Duds/OI-Piranha/10. Frame/Battery frame.png

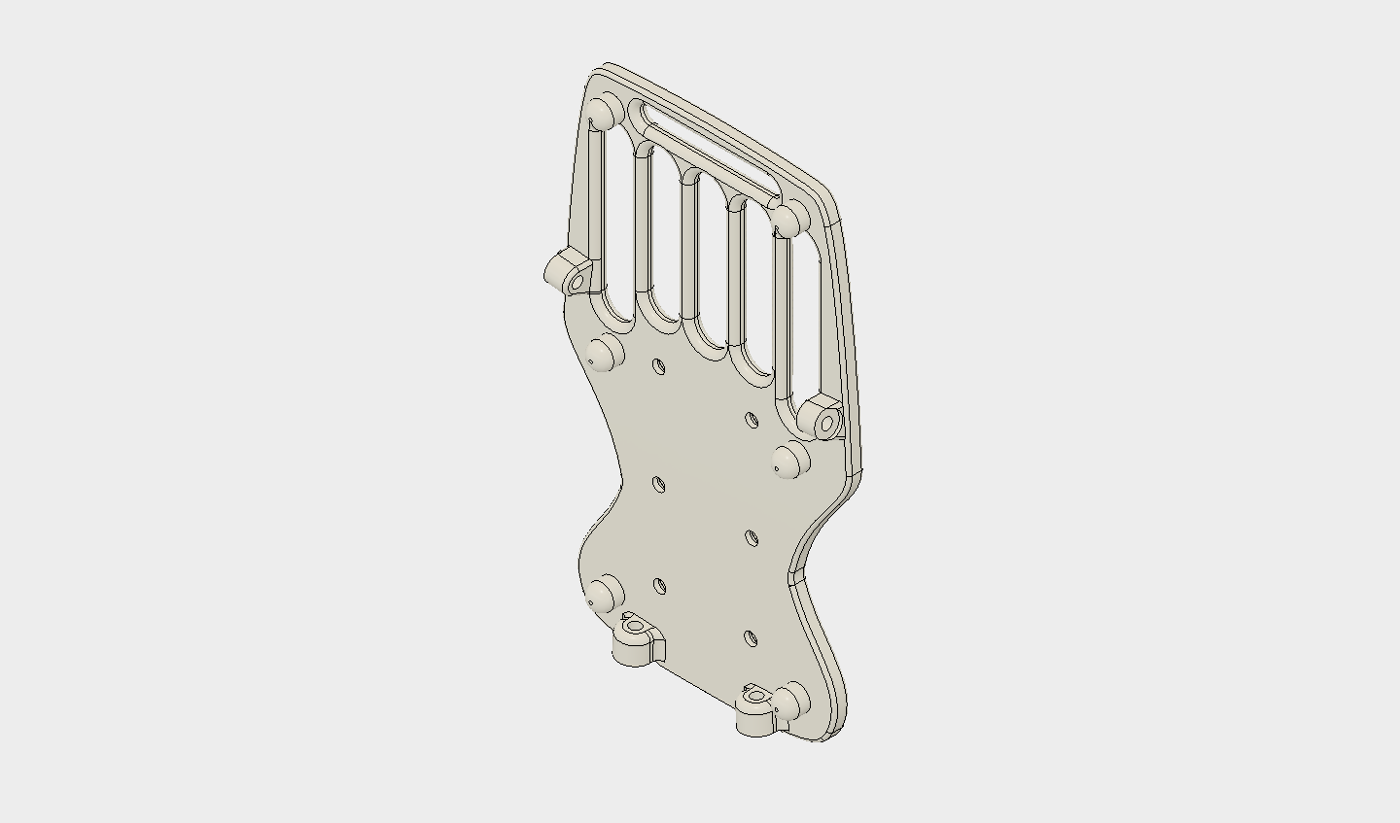
10. Frame/Battery frame.png
