Duds/OI-Piranha/10. Frame/Main frame.png

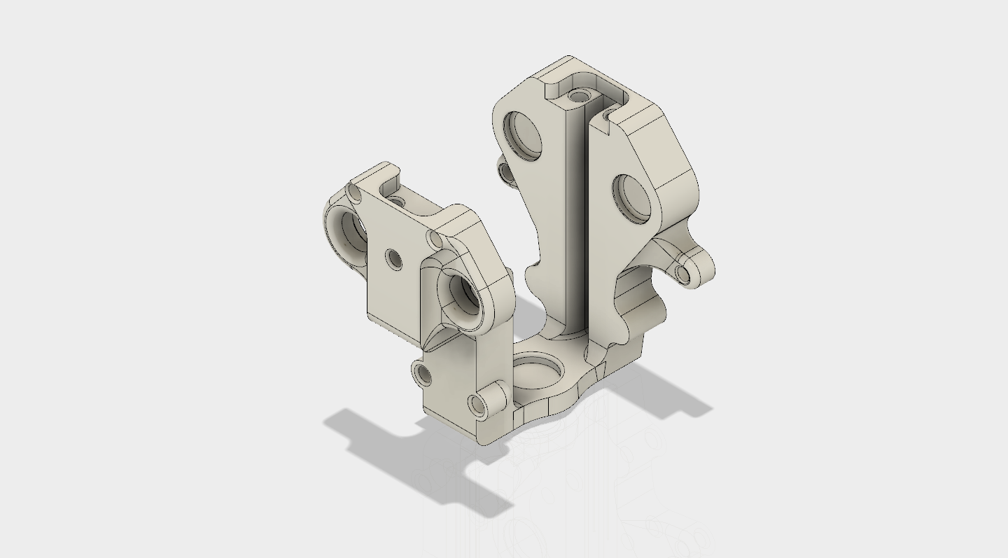
10. Frame/Main frame.png
