Duds/OI-Piranha/10. Frame/Servo Caddy Top Mount.png

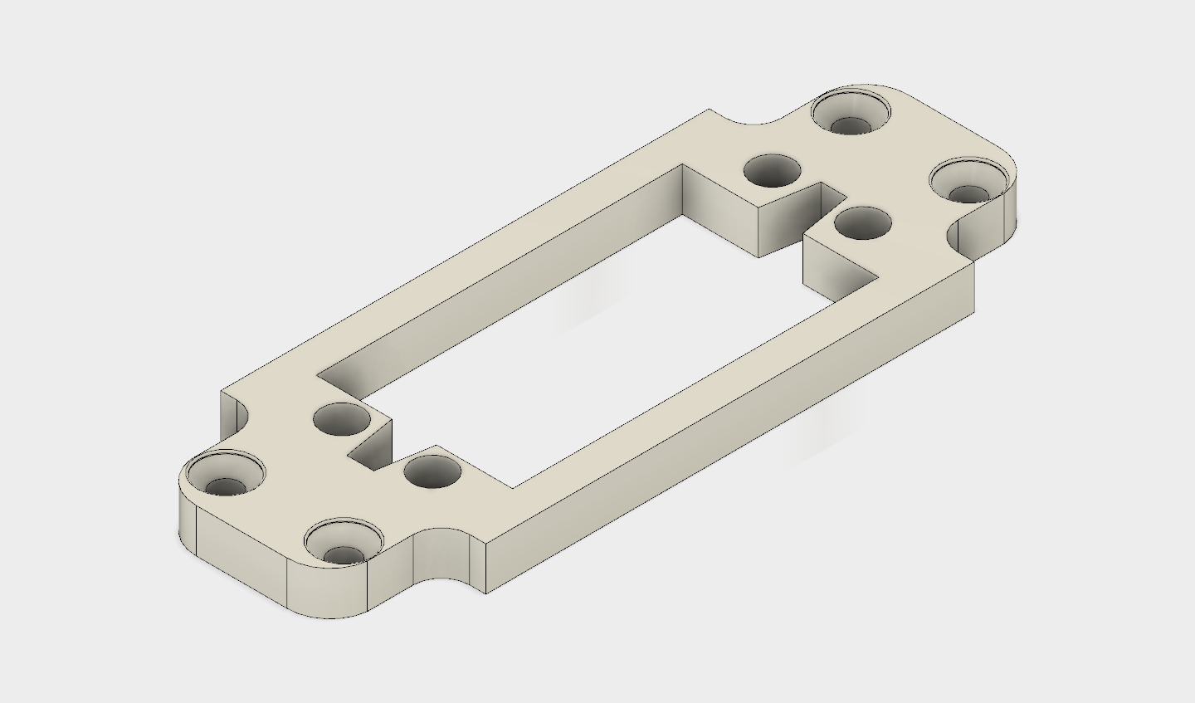
10. Frame/Servo Caddy Top Mount.png
