Duds/OI-Piranha/10. Frame/Servo Caddy.png

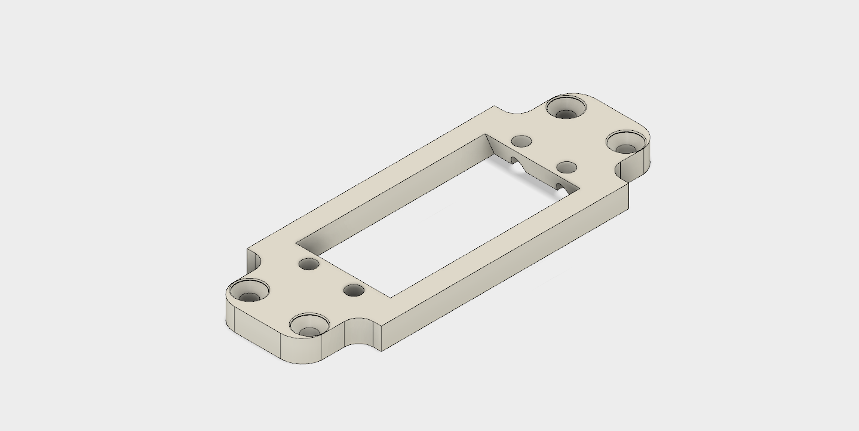
10. Frame/Servo Caddy.png
