Duds/OI-Piranha/20. Body Lift/Lead Screw (buttress thread).png

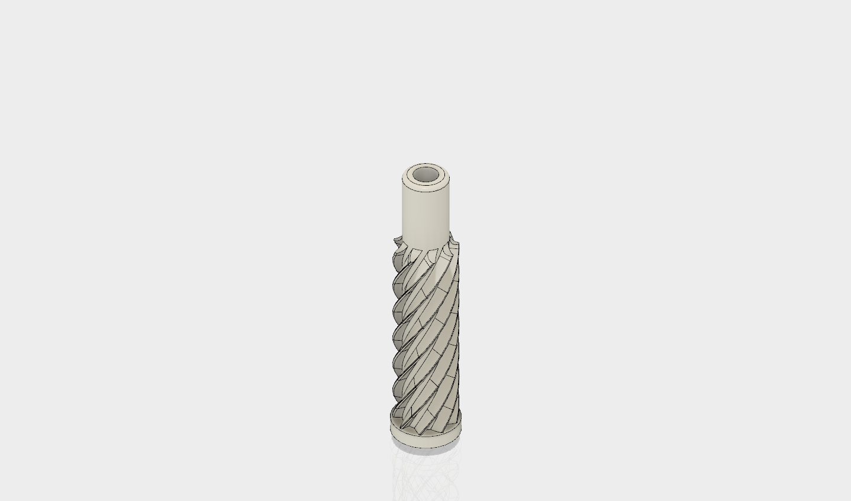
20. Body Lift/Lead Screw (buttress thread).png
