Duds/OI-Piranha/20. Body Lift/Lifting Beam (buttress thread).png

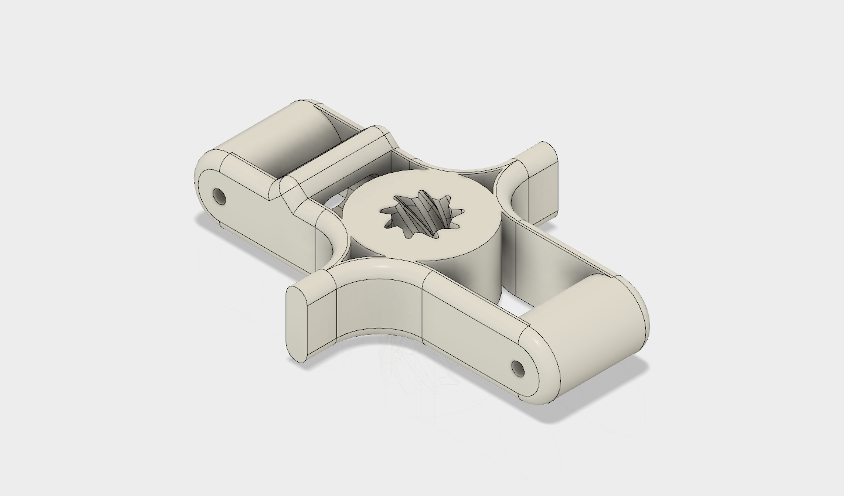
20. Body Lift/Lifting Beam (buttress thread).png
