Duds/OI-Piranha/20. Body Lift/Lifting beam.png

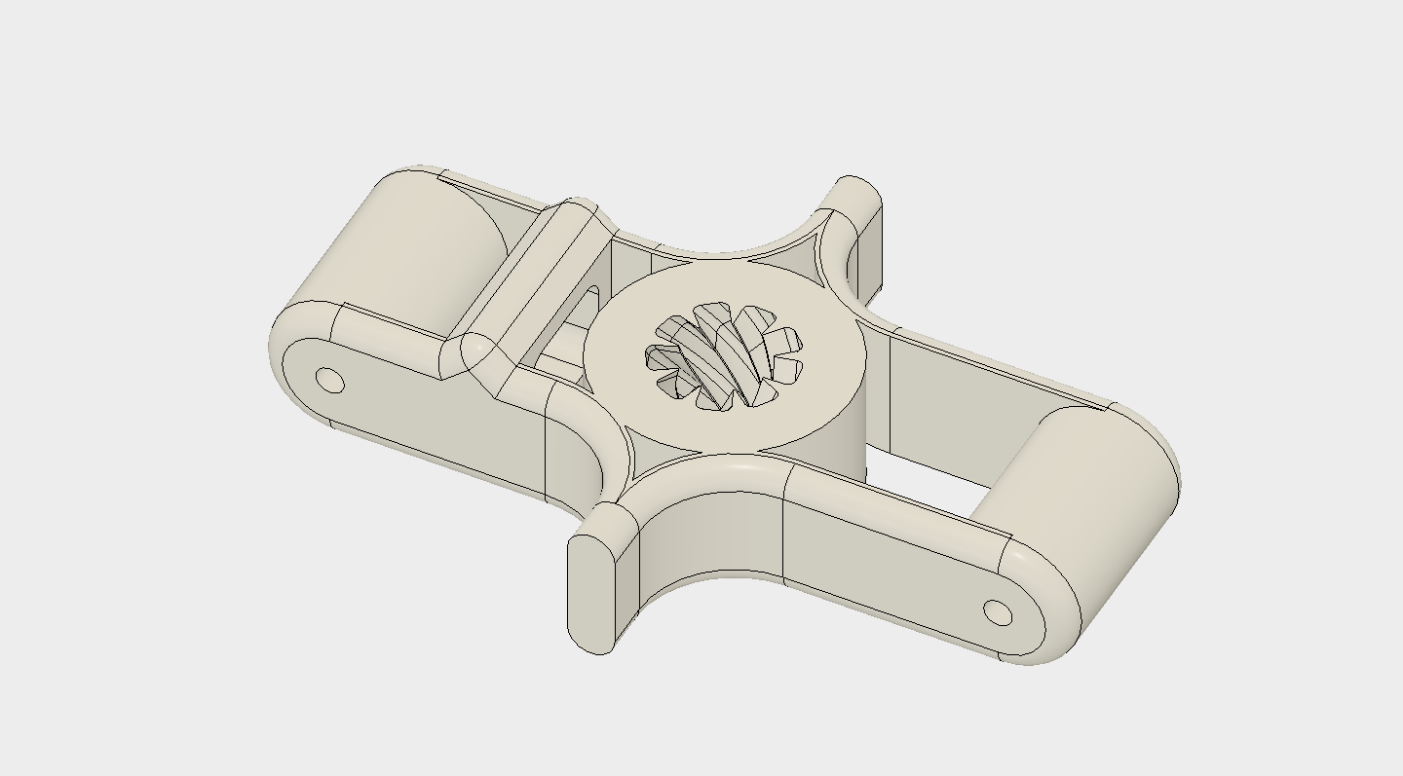
20. Body Lift/Lifting beam.png
