Duds/OI-Piranha/20. Body Lift/Nut die.png

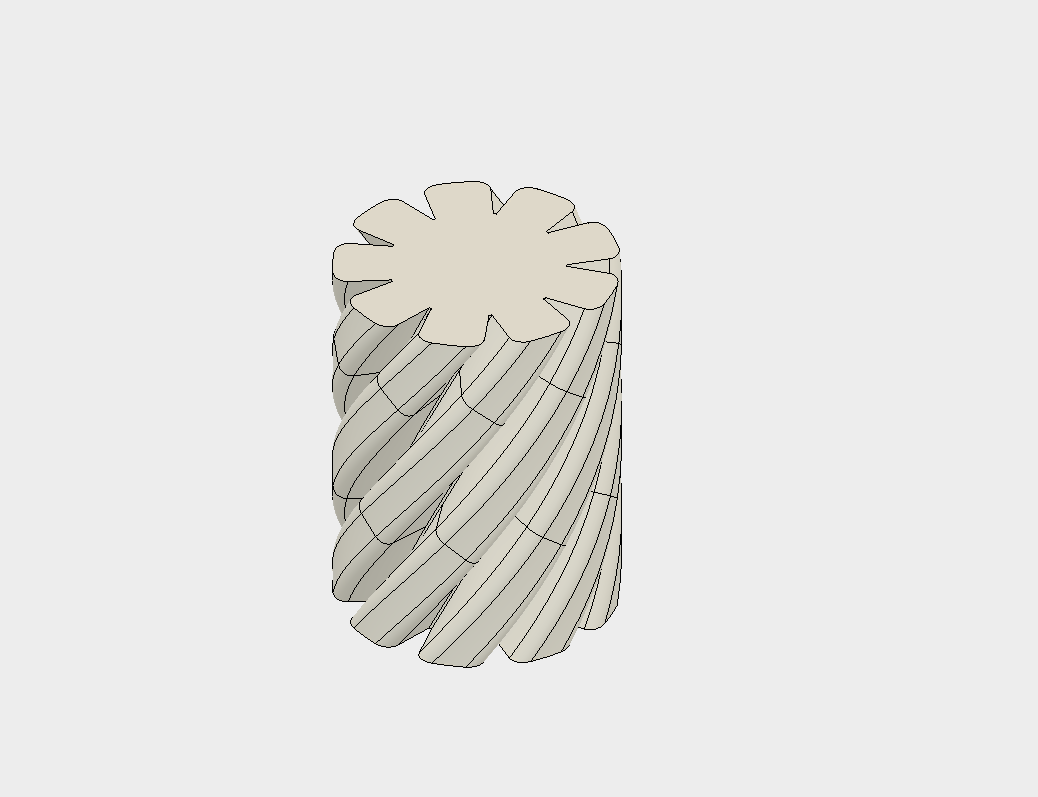
20. Body Lift/Nut die.png
