Duds/OI-Piranha/30. Booms/Landing gear pivot.png

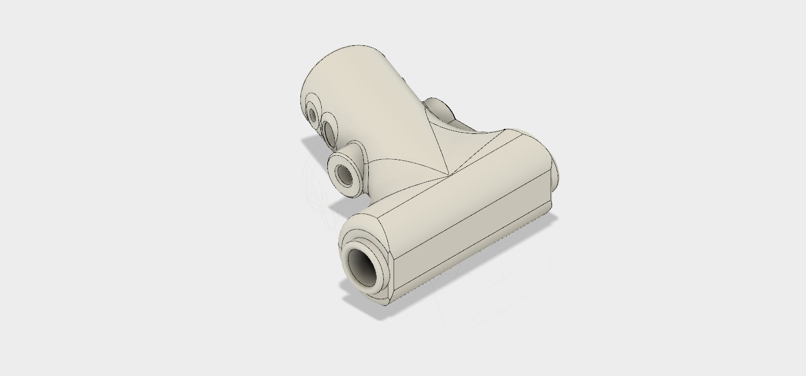
30. Booms/Landing gear pivot.png
