Duds/OI-Piranha/30. Booms/Lift linkage A.png

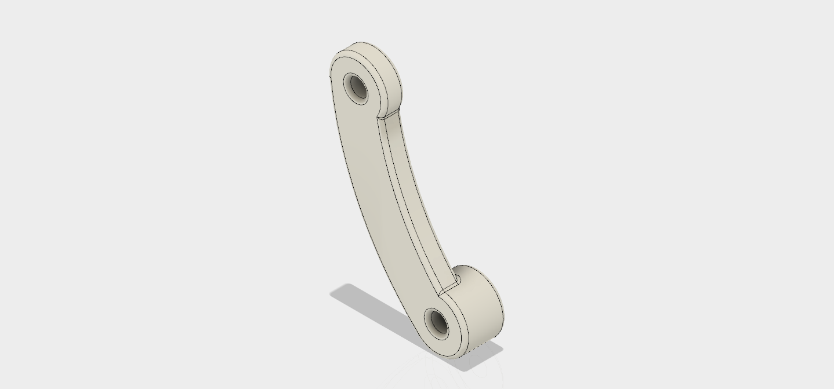
30. Booms/Lift linkage A.png
