Duds/OI-Piranha/50. Fairings/50.1 two part fairing/Bash Plate Two Part.png

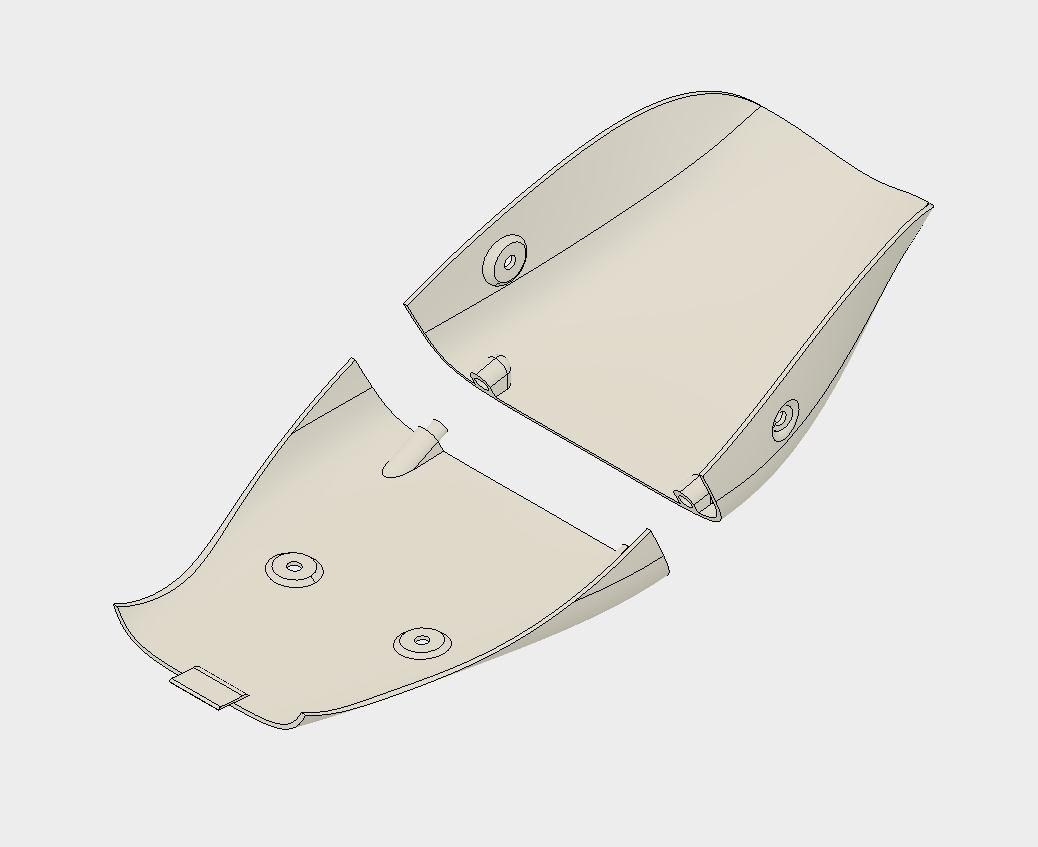
50. Fairings/50.1 two part fairing/Bash Plate Two Part.png
