Duds/OI-Piranha/50. Fairings/50.1 two part fairing/Nose fairing two part no 2.png

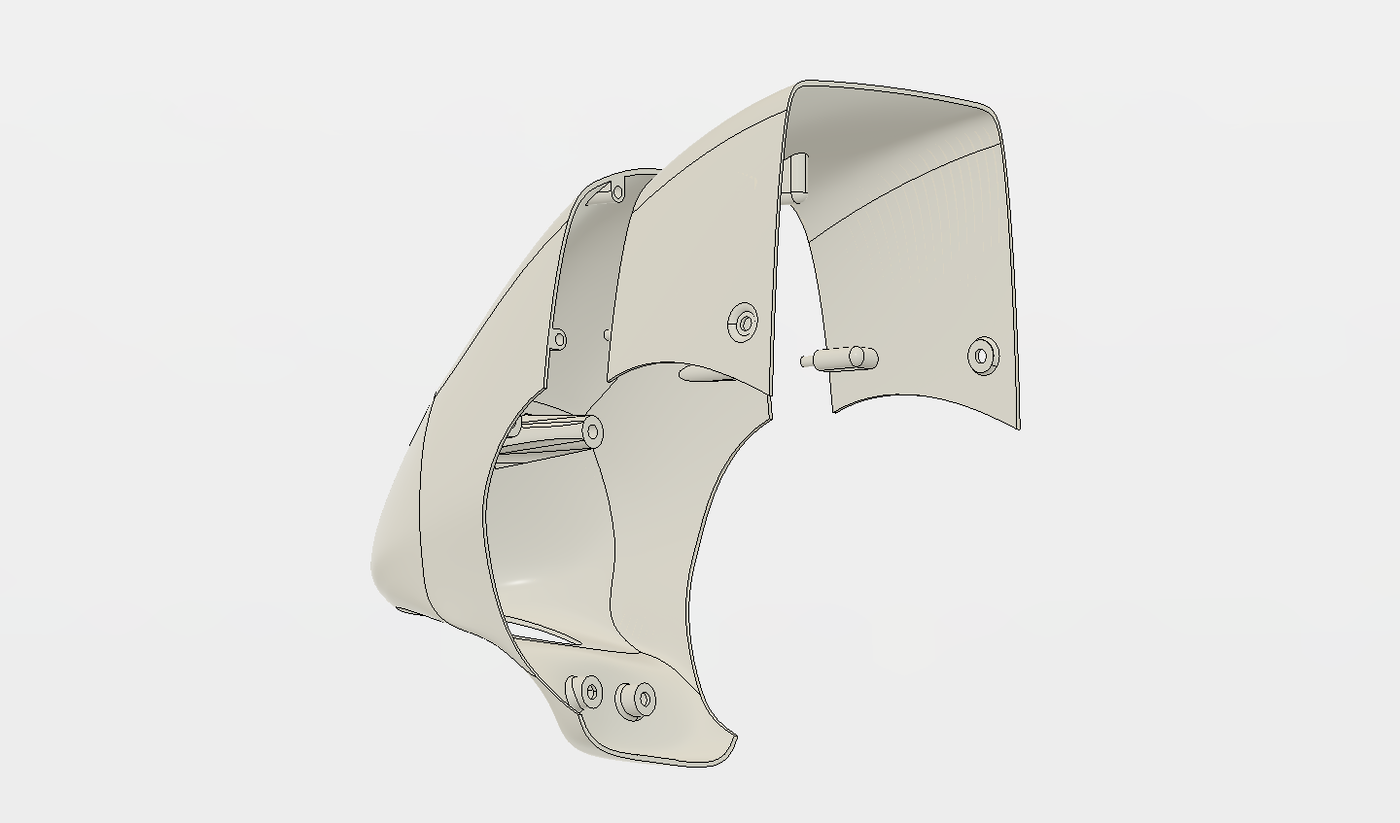
50. Fairings/50.1 two part fairing/Nose fairing two part no 2.png
