Duds/OI-Piranha/50. Fairings/Bash Plate.png

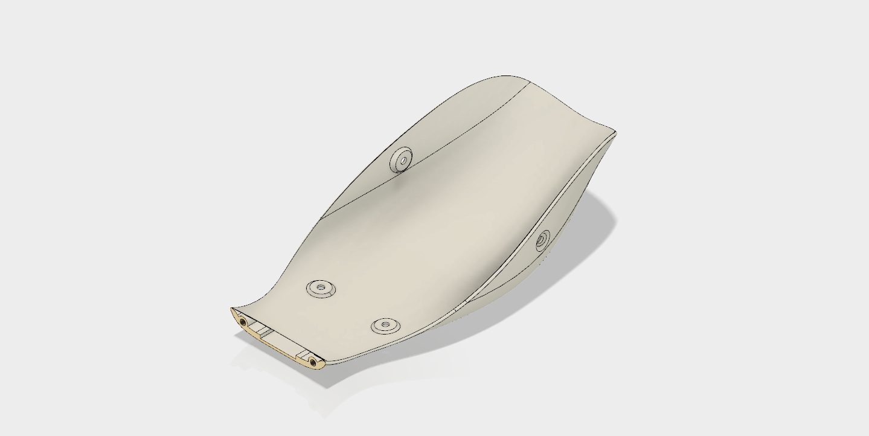
50. Fairings/Bash Plate.png
