Duds/OI-Piranha/50. Fairings/Battery fairing.png

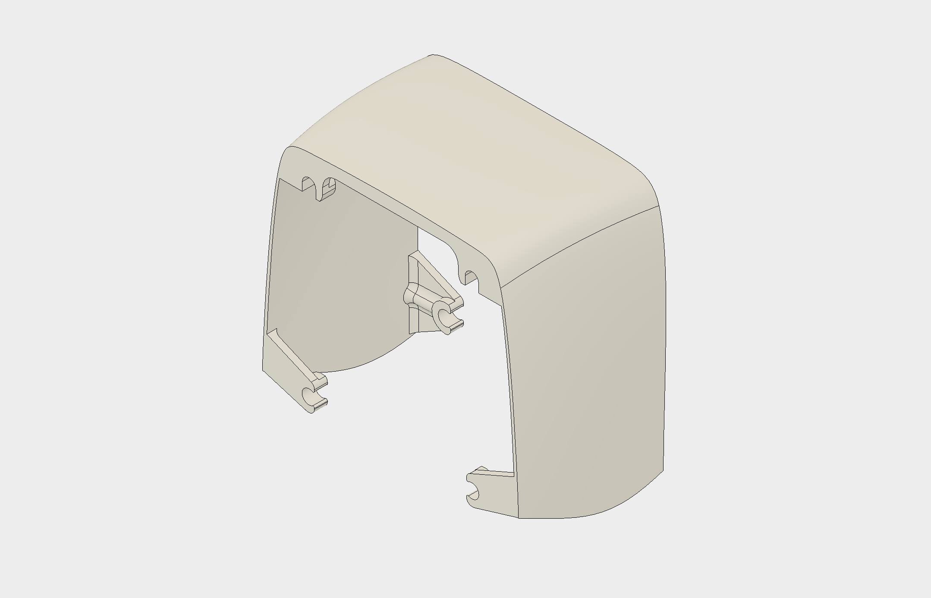
50. Fairings/Battery fairing.png
