Duds/OI-Piranha/50. Fairings/Expansion fairing.png

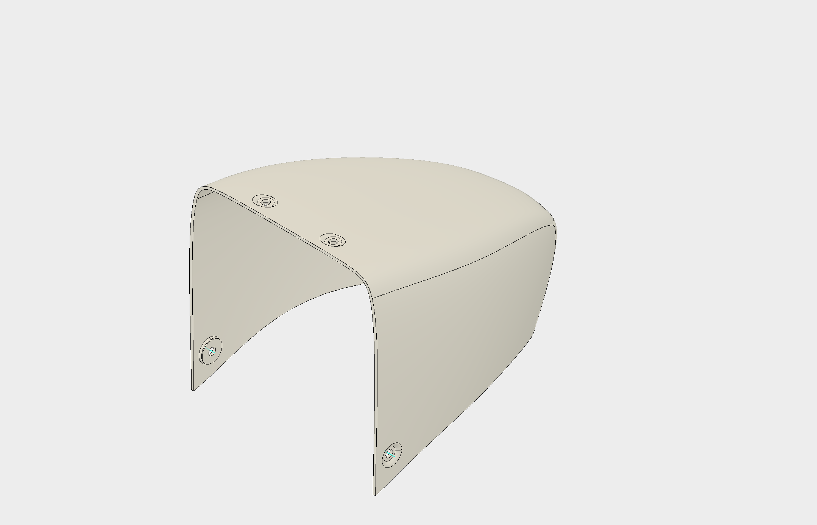
50. Fairings/Expansion fairing.png
