Duds/OI-Piranha/50. Fairings/Nose Fairing.png

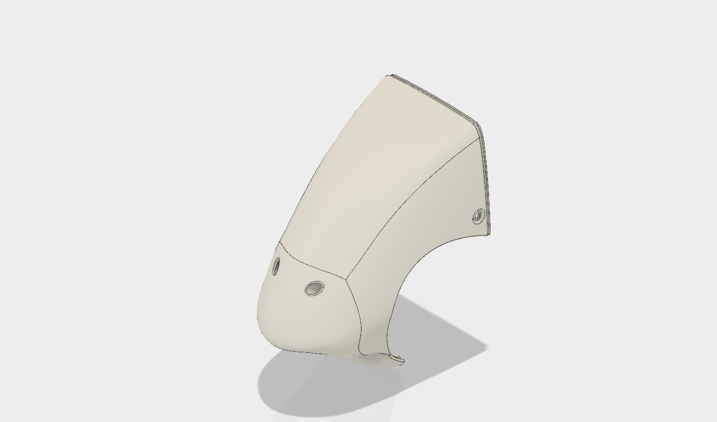
50. Fairings/Nose Fairing.png
