Duds/OI-Piranha/60. Payload/Gimbal support.png

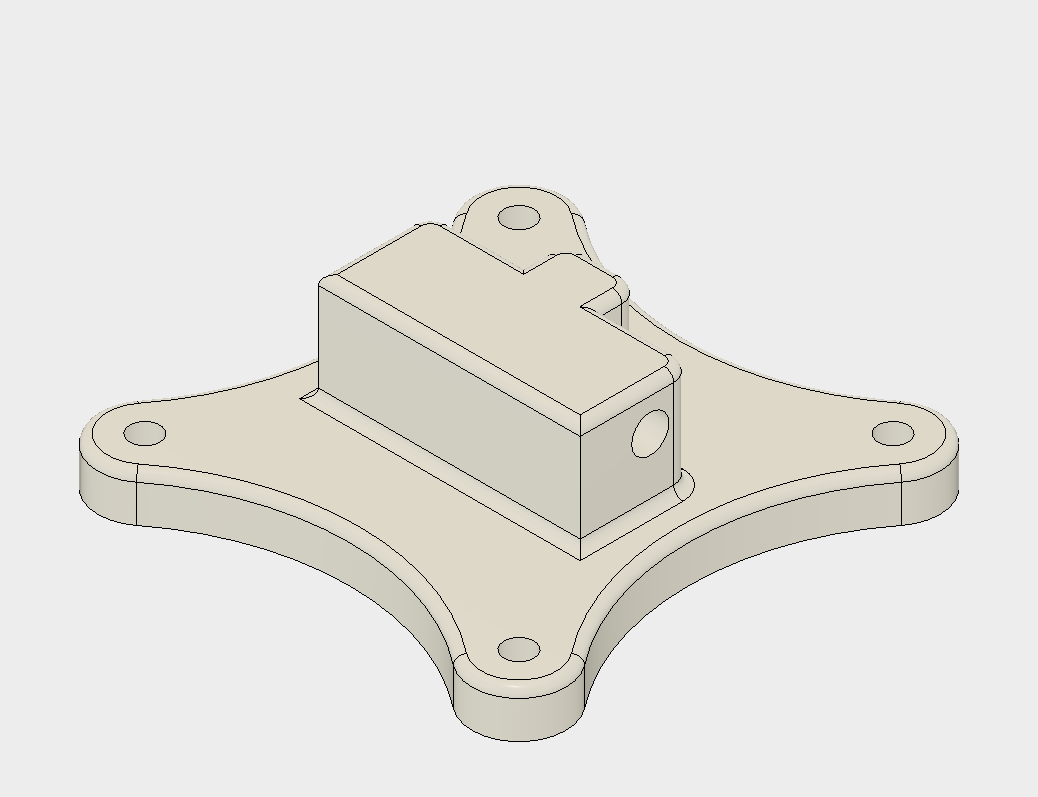
60. Payload/Gimbal support.png
