Duds/OI-Piranha/200. Renders/OI Pirahna expansion shelves.png

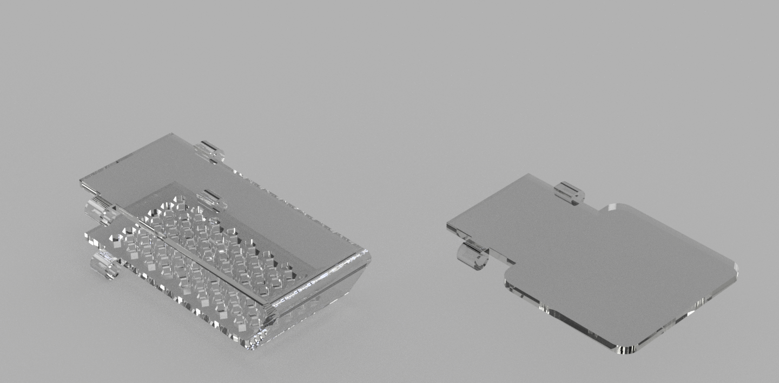
200. Renders/OI Pirahna expansion shelves.png
