Duds/OI-Piranha/200. Renders/OI Pirahna Main frame, caddy and servo.png

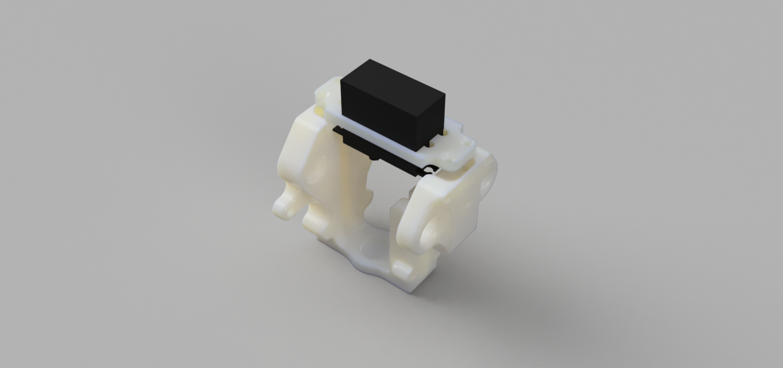
200. Renders/OI Pirahna Main frame, caddy and servo.png
