Duds/OI-Piranha/200. Renders/OI Piranha battery and accessory fairing removed 2.png

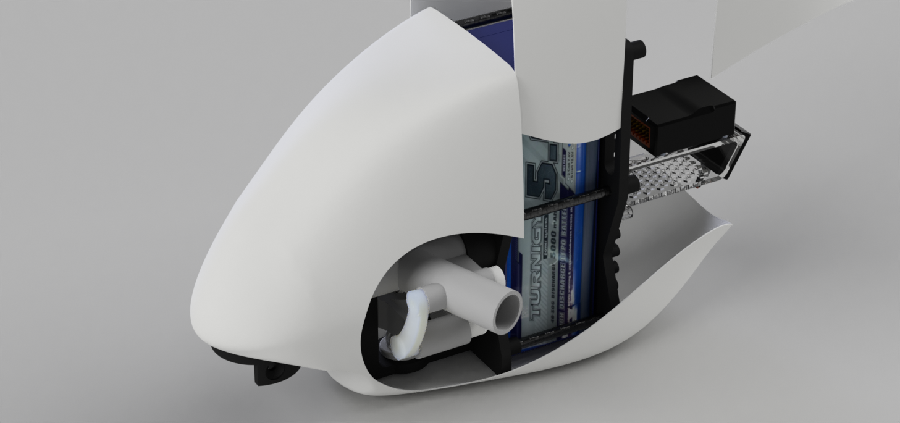
200. Renders/OI Piranha battery and accessory fairing removed 2.png
