Duds/OI-Piranha/200. Renders/OI Piranha battery and accessory fairing removed.png

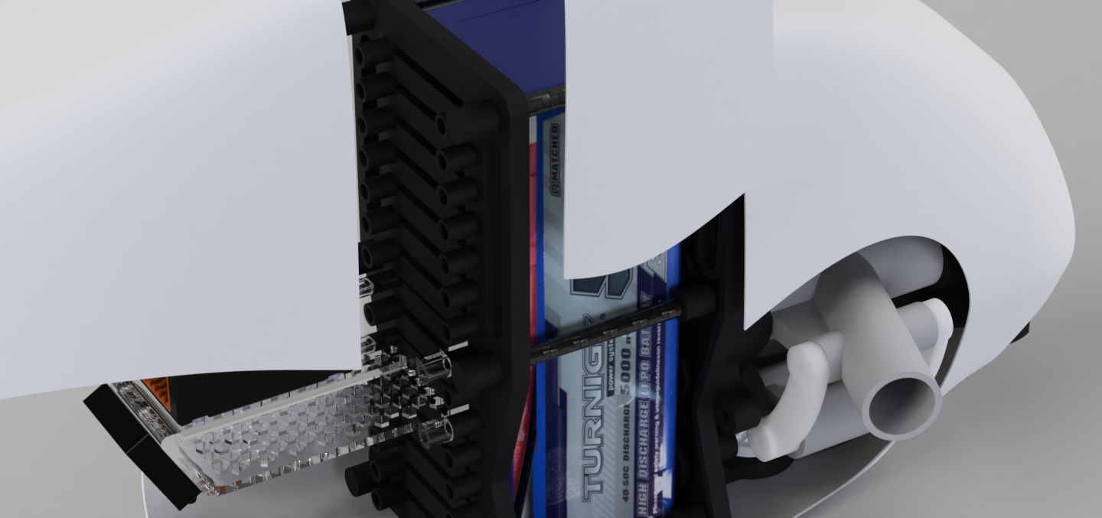
200. Renders/OI Piranha battery and accessory fairing removed.png
