Duds/OI-Piranha/200. Renders/OI Piranha body lift mechanism closeup.png

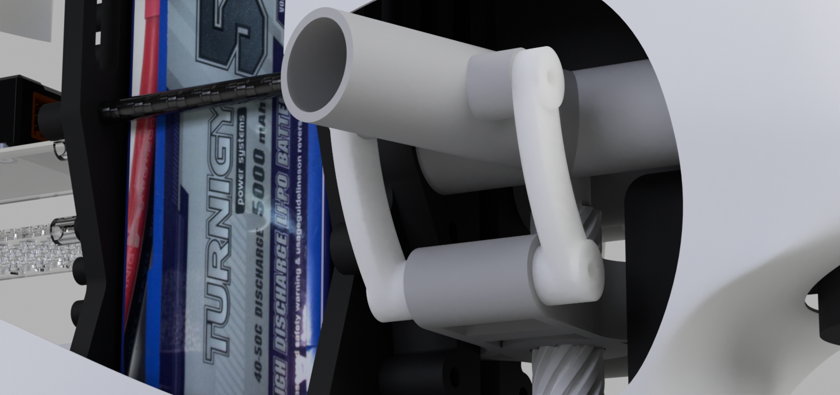
200. Renders/OI Piranha body lift mechanism closeup.png
