Duds/OI-Piranha/200. Renders/OI Piranha close up of NAZA accessory shelf.png

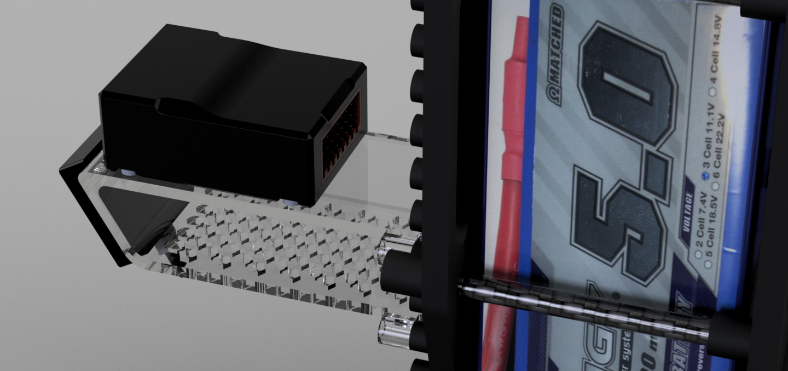
200. Renders/OI Piranha close up of NAZA accessory shelf.png
