Duds/OI-Piranha/200. Renders/OI Piranha closeup NAZA accessory shelf.png

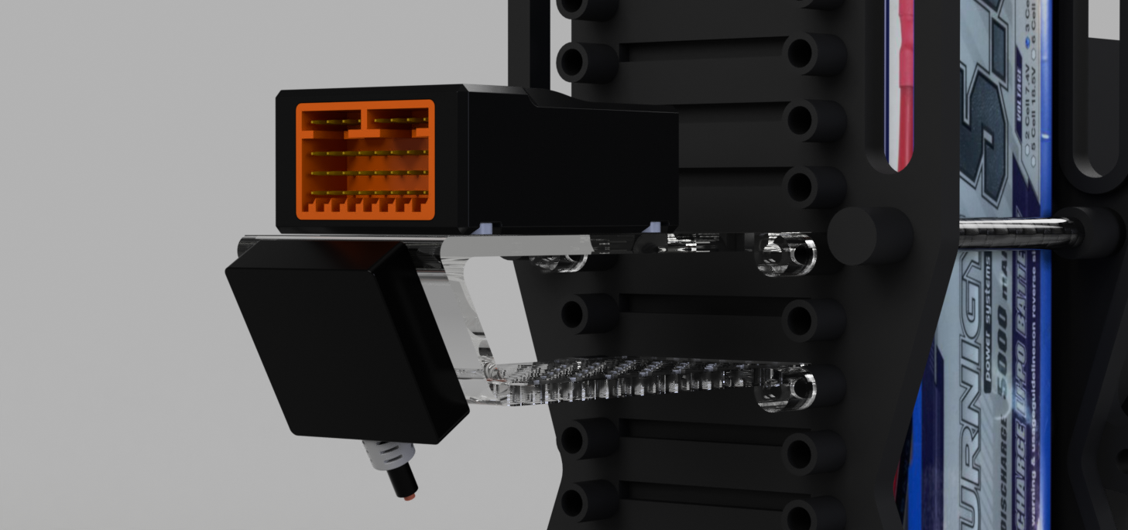
200. Renders/OI Piranha closeup NAZA accessory shelf.png
