Duds/OI-Piranha/200. Renders/OI Piranha Fairings removed.png

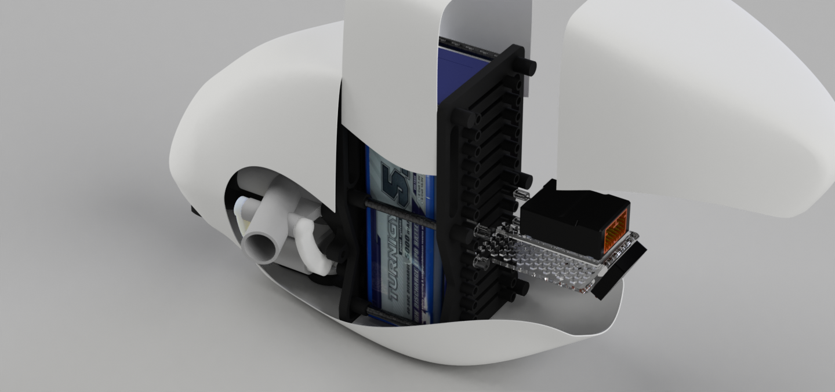
200. Renders/OI Piranha Fairings removed.png
