Duds/OI-Piranha/200. Renders/OI Piranha Frame.png

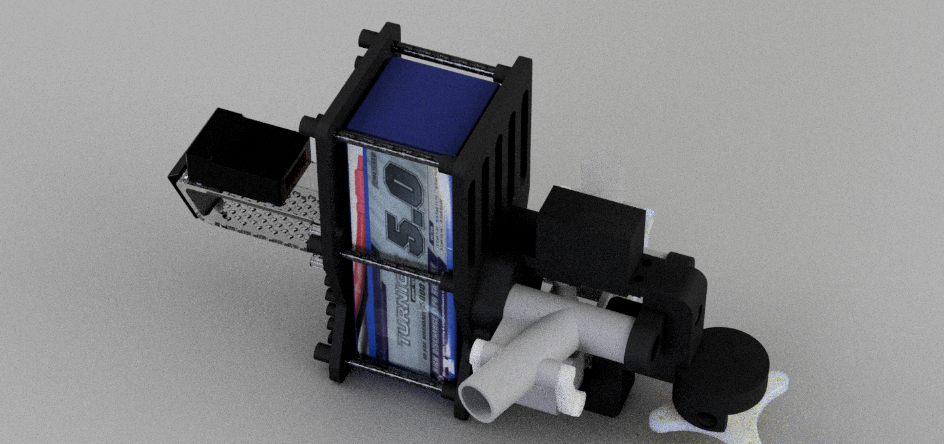
200. Renders/OI Piranha Frame.png
