Duds/OI-Piranha/200. Renders/OI Piranha open frame front.png

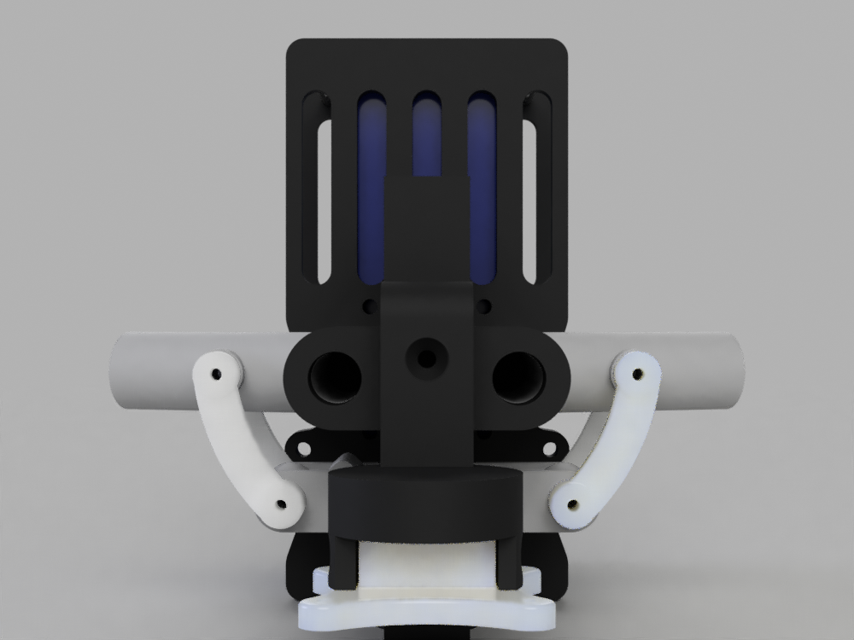
200. Renders/OI Piranha open frame front.png
