Duds/OI-Piranha/200. Renders/OI Piranha open frame side top view.png

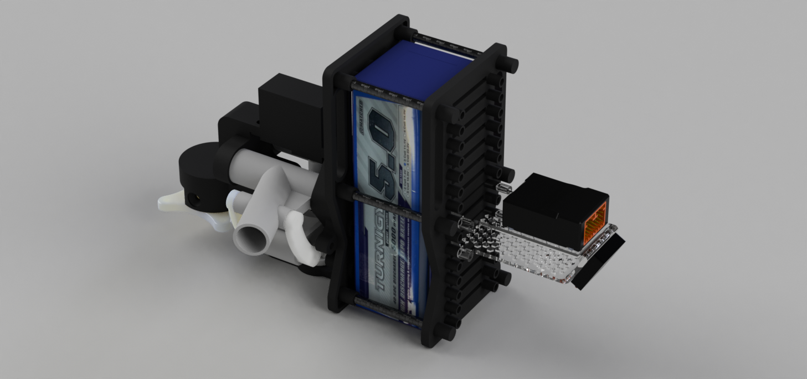
200. Renders/OI Piranha open frame side top view.png
