Duds/OI-Piranha/200. Renders/OI Piranha side view top down.png

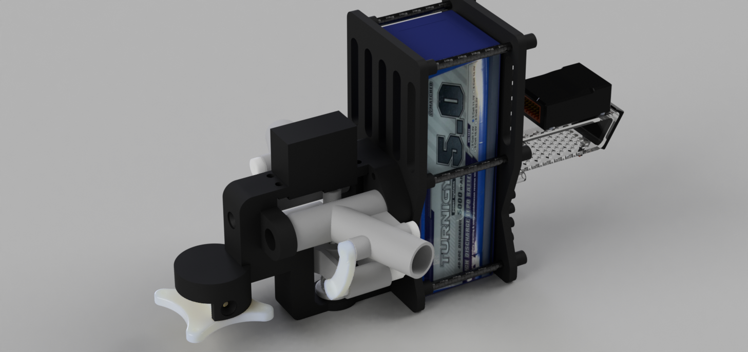
200. Renders/OI Piranha side view top down.png
