Duds/OI-Piranha/200. Renders/OI Piranha v0.3.0 Release image 8.png

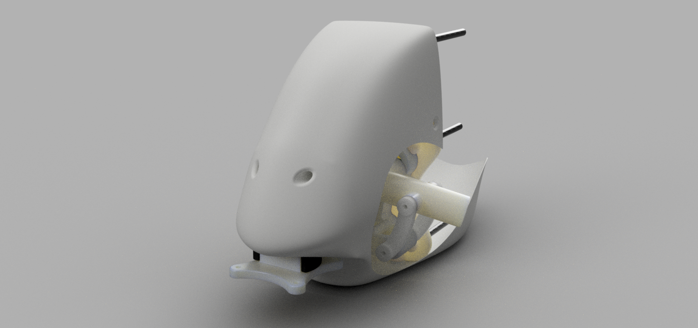
200. Renders/OI Piranha v0.3.0 Release image 8.png
