Duds/OI-Piranha/200. Renders/OI Piranha with fairing on.png

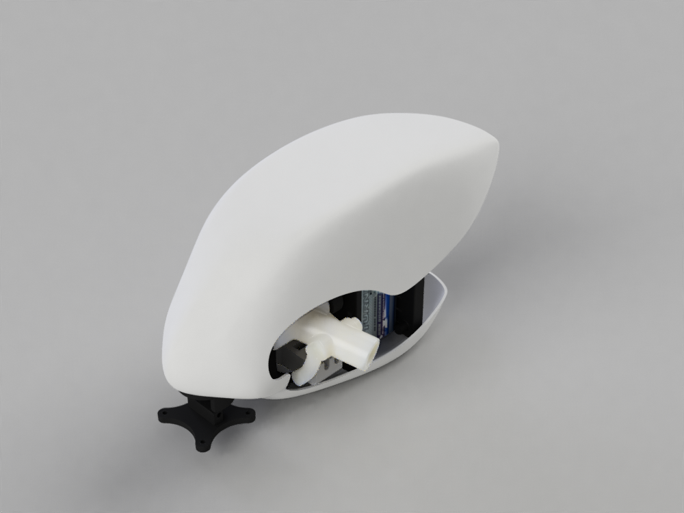
200. Renders/OI Piranha with fairing on.png
