Duds/OI-Piranha/40. Expansion Parts/Basic Expansion Shelf.png

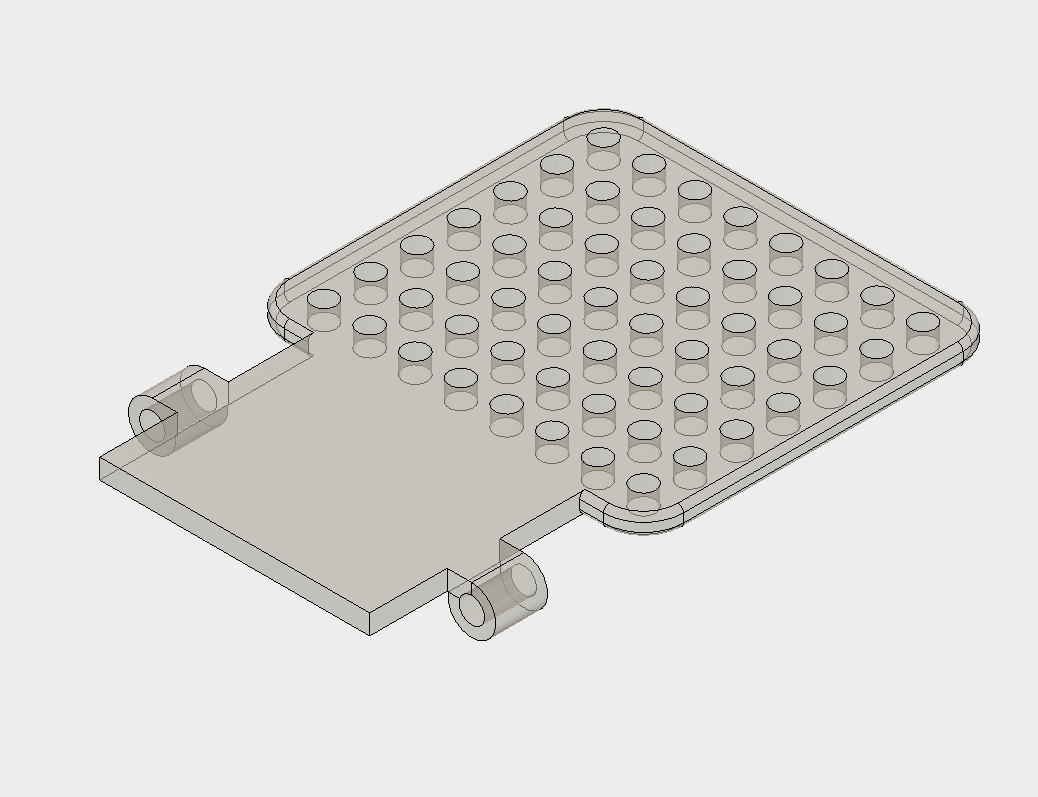
40. Expansion Parts/Basic Expansion Shelf.png
