Duds/OI-Piranha/30. Booms/Landing gear pivot.step

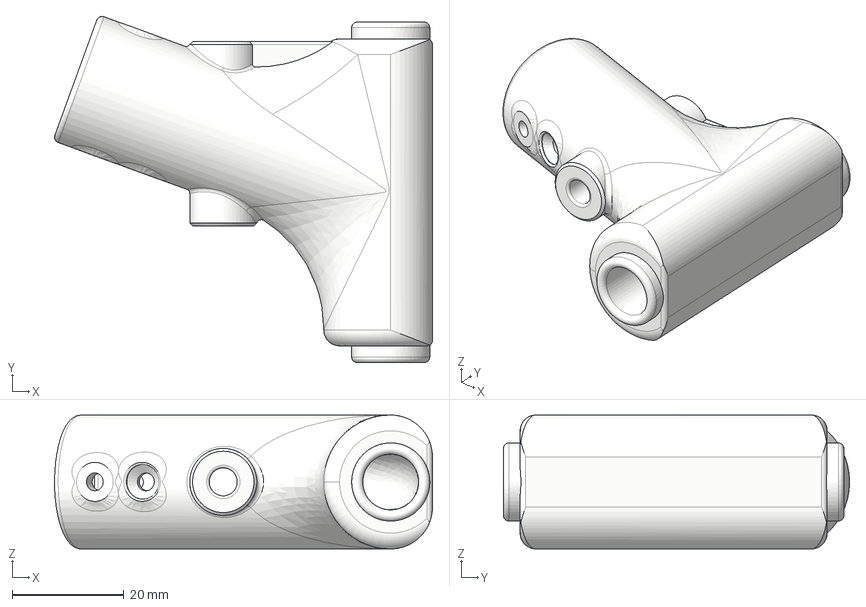
[picture p59: CAD file, 2016-10-27]
30. Booms/Landing gear pivot.step
67.7 x 62.0 x 24.0 mm
