Duds/OI-Piranha/40. Expansion Parts/Basic Expansion Shelf.step

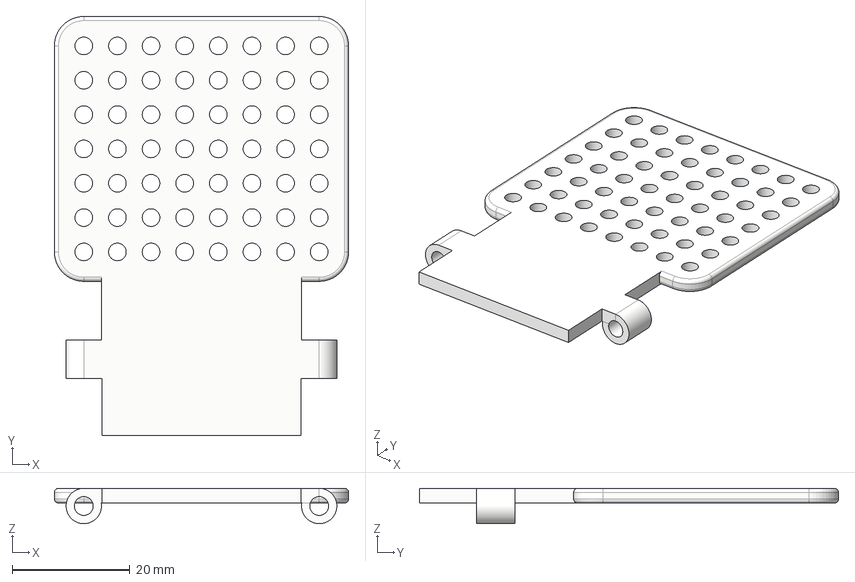
[picture p60: CAD file, 2016-10-15]
40. Expansion Parts/Basic Expansion Shelf.step
50.0 x 71.2 x 6.00 mm
