Duds/OI-Piranha/50. Fairings/50.1 two part fairing/Bash Plate part A.stl

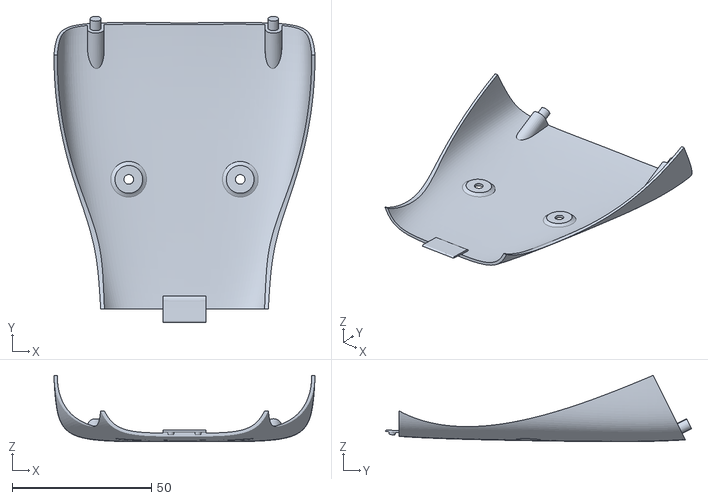
[picture p61: CAD file, 2016-10-15]
50. Fairings/50.1 two part fairing/Bash Plate part A.stl
93.8 x 110.1 x 23.8
