Duds/OI-Piranha/50. Fairings/Battery fairing.step

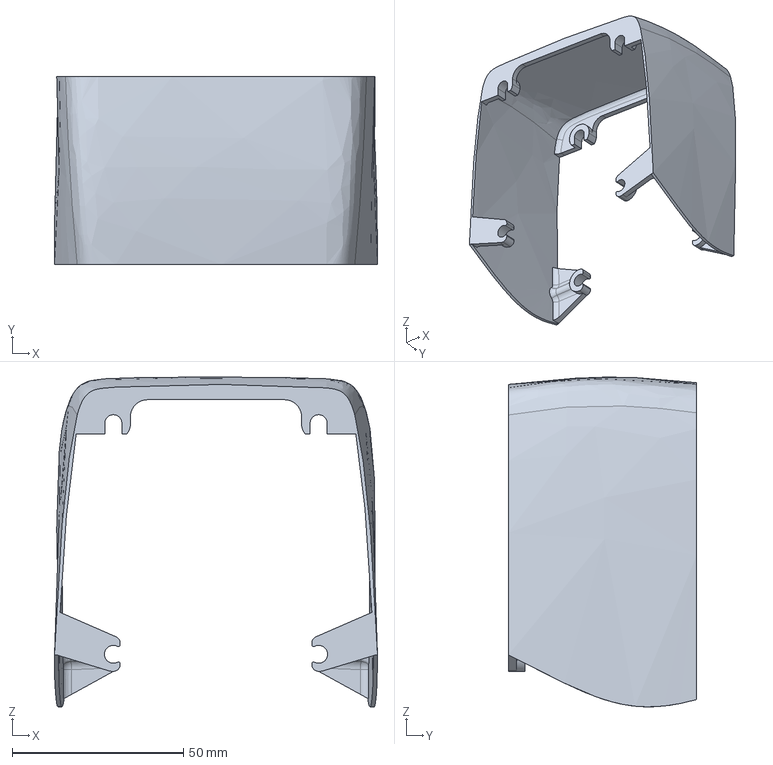
[picture p62: CAD file, 2016-10-15]
50. Fairings/Battery fairing.step
94.4 x 55.0 x 96.4 mm
