Duds/OI-Piranha/10. Frame/10.1 Two Part Frames (for smaller print volumes)/Lifting beam.step

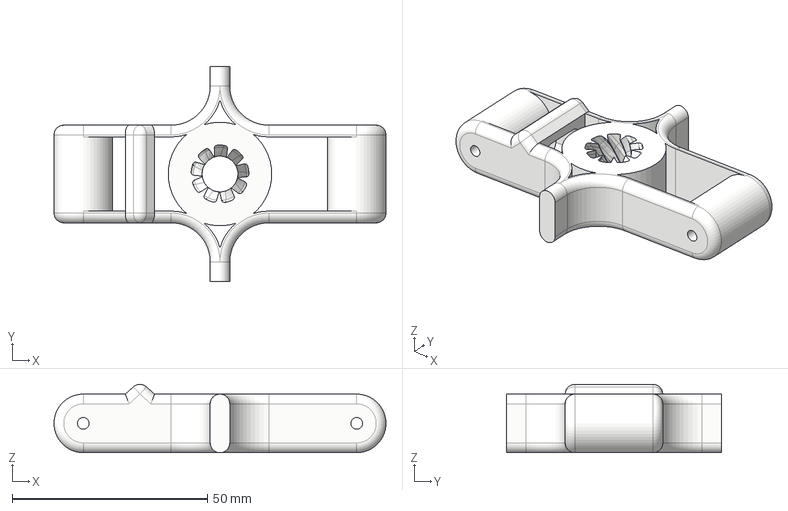
[picture p63: CAD file, 2016-10-15]
10. Frame/10.1 Two Part Frames (for smaller print volumes)/Lifting beam.step
85.0 x 55.0 x 17.5 mm
