Duds/OI-Piranha/10. Frame/Servo Caddy Top Mount.step

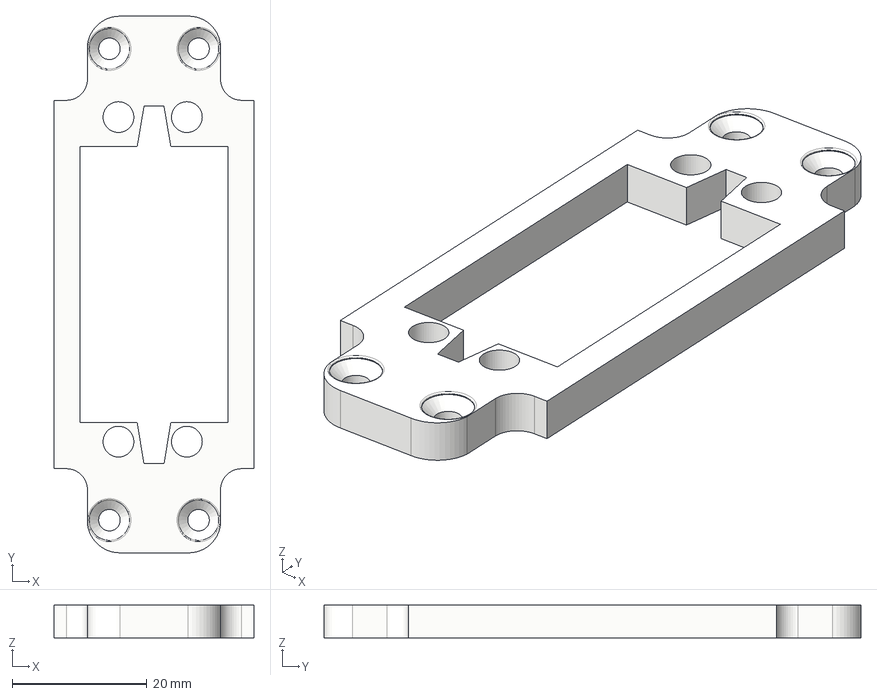
[picture p64: CAD file, 2016-10-27]
10. Frame/Servo Caddy Top Mount.step
29.7 x 79.7 x 4.90 mm
