Duds/OI-Piranha/40. Expansion Parts/DJI NAZA system expansion shelf.step

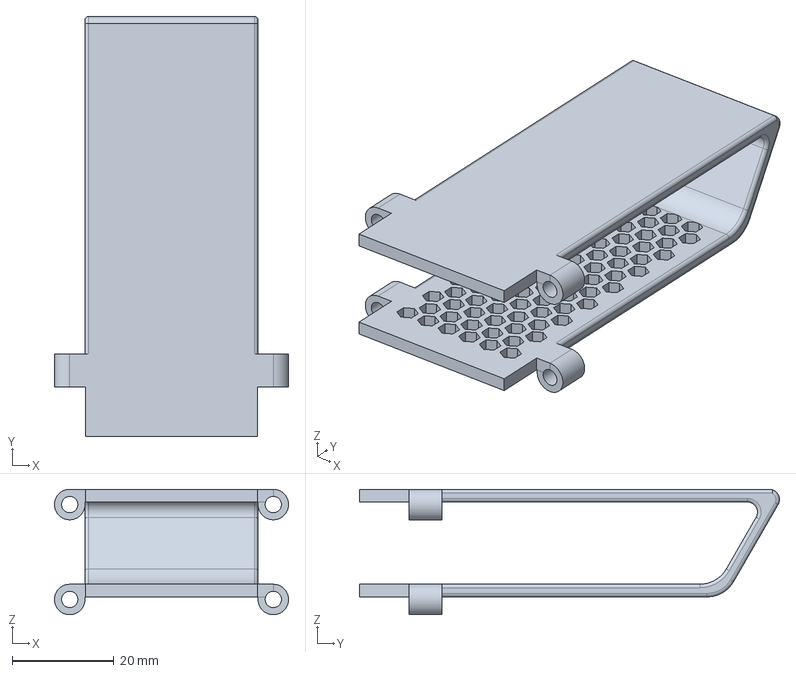
[picture p65: CAD file, 2016-10-15]
40. Expansion Parts/DJI NAZA system expansion shelf.step
46.0 x 82.5 x 24.6 mm
