Duds/OI-Piranha/50. Fairings/50.1 two part fairing/Bash Plate part B.stl

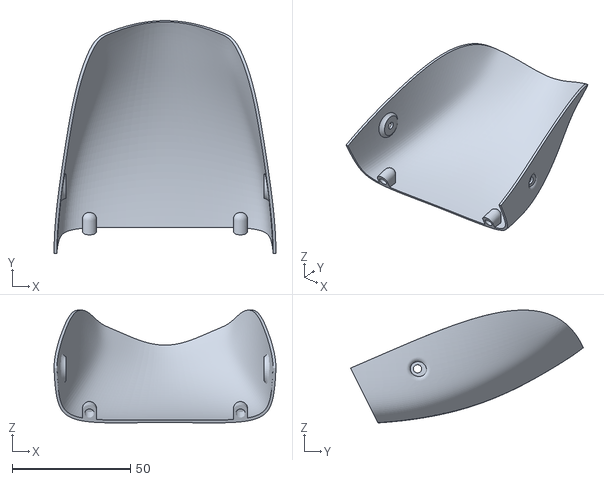
[picture p66: CAD file, 2016-10-15]
50. Fairings/50.1 two part fairing/Bash Plate part B.stl
93.8 x 98.3 x 47.7
