Duds/OI-Piranha/50. Fairings/Expansion fairing.step

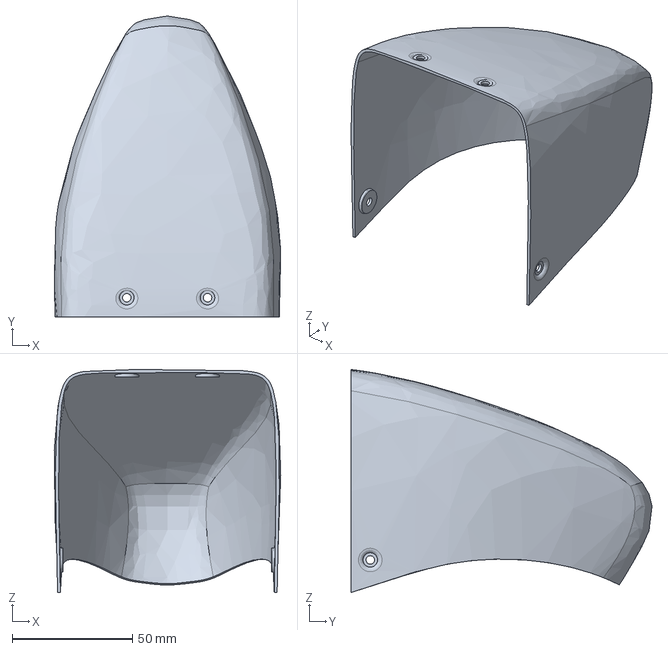
[picture p67: CAD file, 2016-10-15]
50. Fairings/Expansion fairing.step
94.0 x 124.9 x 92.6 mm
