Duds/OI-Piranha/10. Frame/10.1 Two Part Frames (for smaller print volumes)/Battery Frame Part B.stl

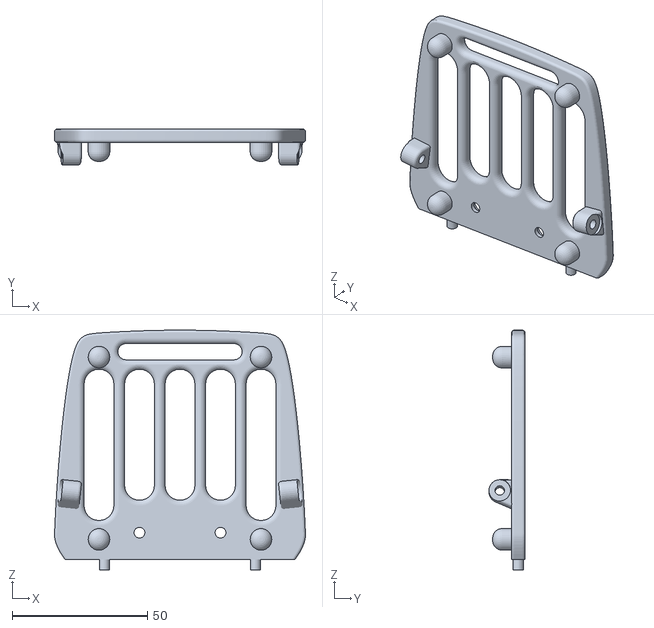
[picture p68: CAD file, 2016-10-15]
10. Frame/10.1 Two Part Frames (for smaller print volumes)/Battery Frame Part B.stl
93.0 x 13.4 x 88.8
