Duds/OI-Piranha/10. Frame/Gimbal Support Frame.step

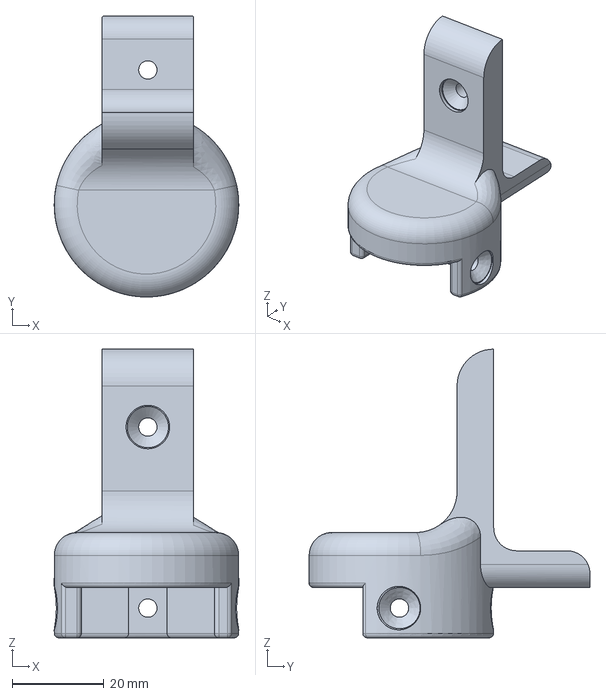
[picture p69: CAD file, 2016-10-15]
10. Frame/Gimbal Support Frame.step
40.3 x 61.3 x 63.0 mm
