Duds/OI-Piranha/50. Fairings/50.1 two part fairing/Nose fairing part 1.stl

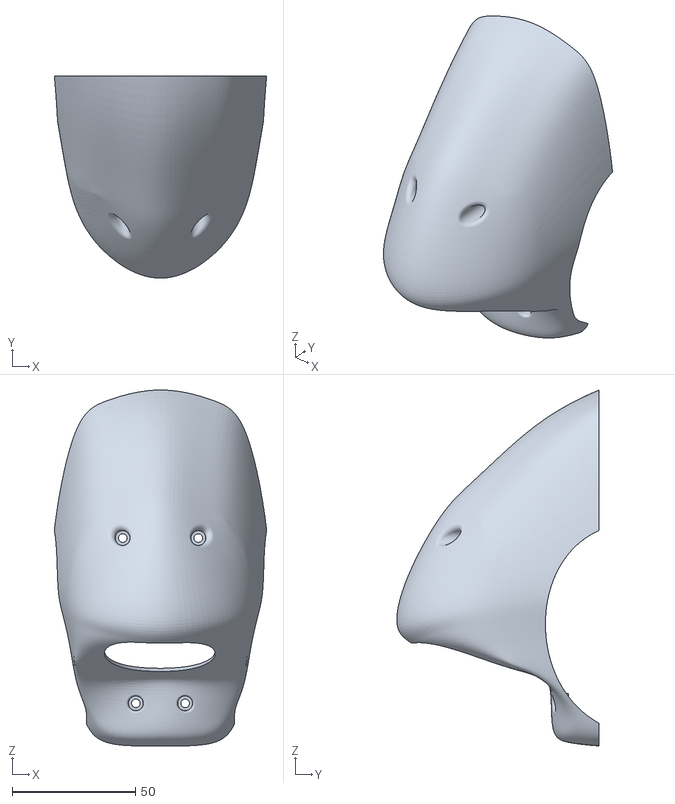
[picture p70: CAD file, 2016-10-11]
50. Fairings/50.1 two part fairing/Nose fairing part 1.stl
86.2 x 82.1 x 144.5
