Duds/OI-Piranha/10. Frame/10.1 Two Part Frames (for smaller print volumes)/Expansion Frame Two Part B.stl

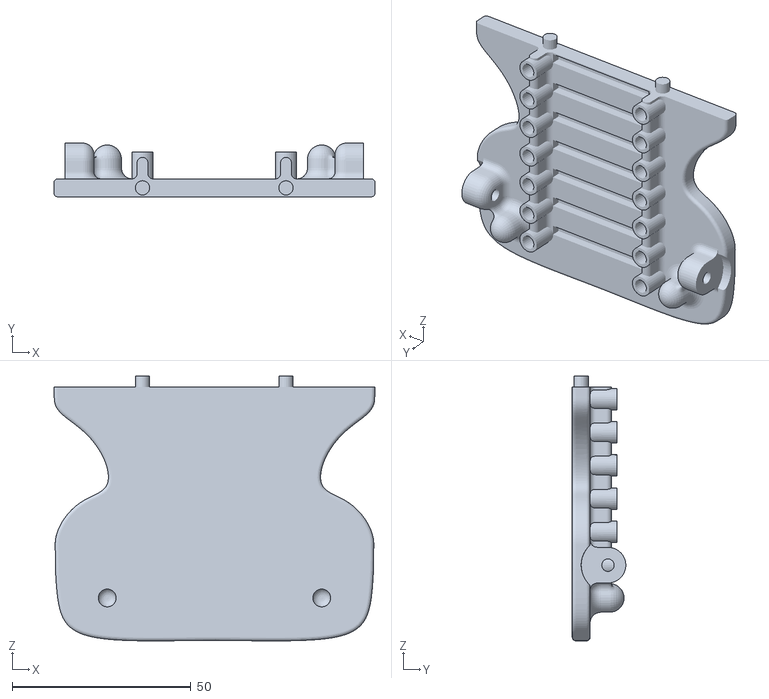
[picture p71: CAD file, 2016-10-11]
10. Frame/10.1 Two Part Frames (for smaller print volumes)/Expansion Frame Two Part B.stl
89.8 x 15.0 x 74.0
