Duds/OI-Piranha/10. Frame/Expansion Frame.step

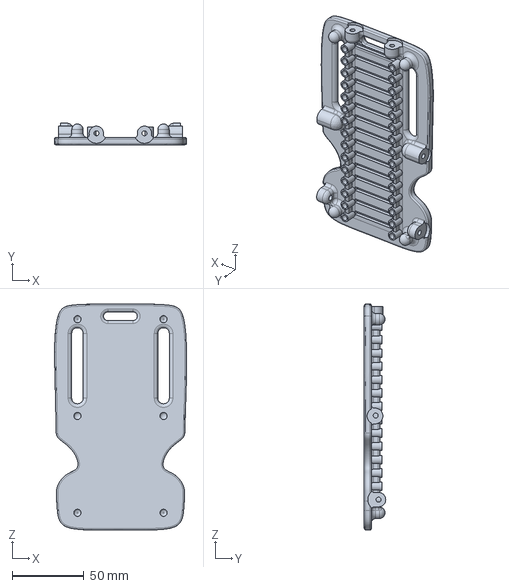
[picture p72: CAD file, 2016-10-15]
10. Frame/Expansion Frame.step
92.2 x 15.0 x 157.6 mm
