Duds/OI-Piranha/50. Fairings/50.1 two part fairing/Nose Fairing part 2.stl

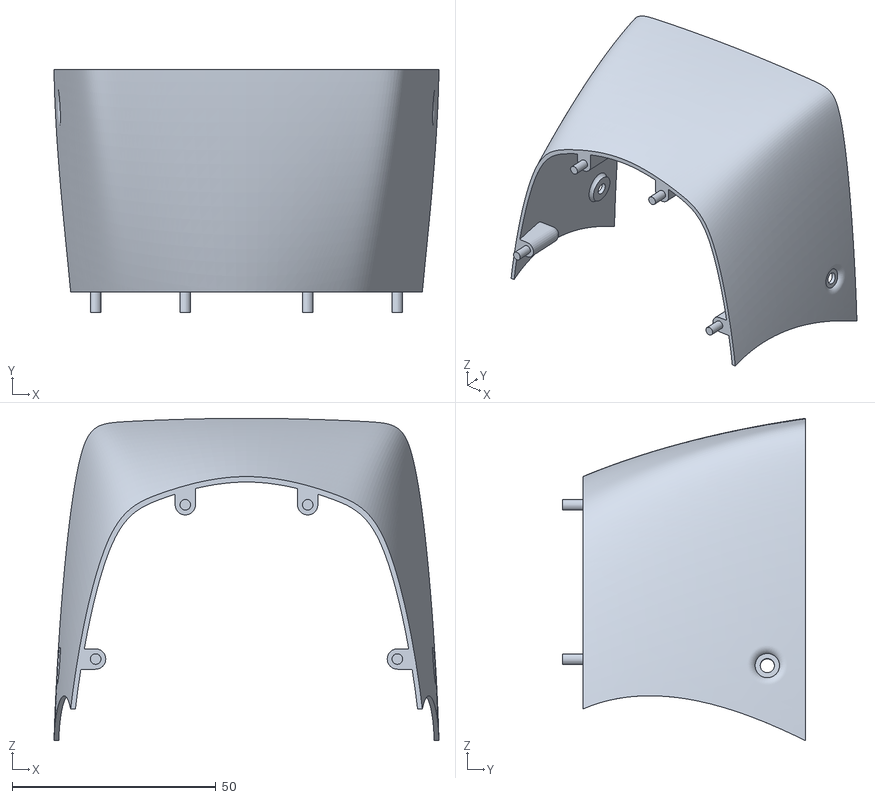
[picture p73: CAD file, 2016-10-11]
50. Fairings/50.1 two part fairing/Nose Fairing part 2.stl
94.4 x 59.6 x 79.0
