Duds/OI-Piranha/10. Frame/10.1 Two Part Frames (for smaller print volumes)/Expansion Frame Two Part A.stl

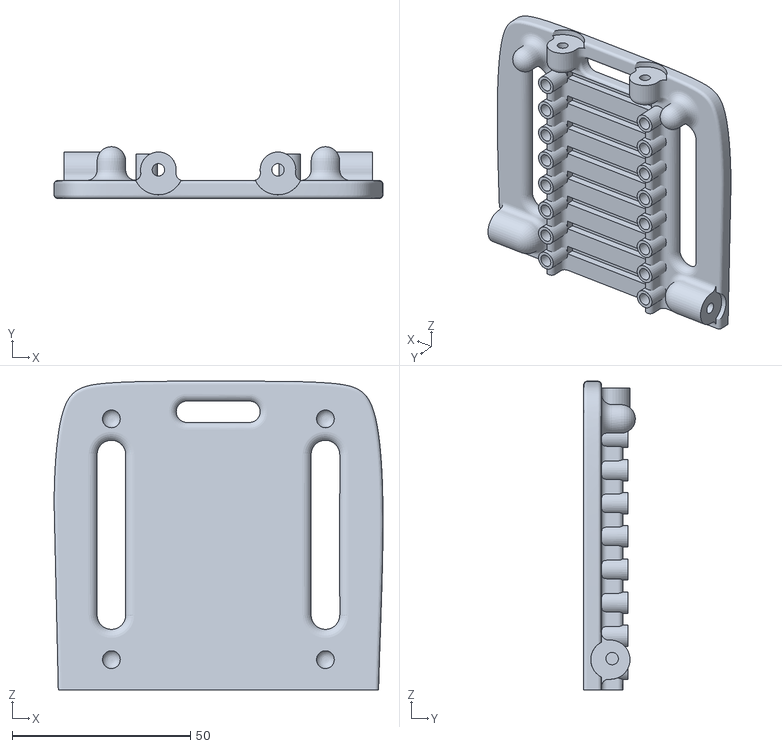
[picture p74: CAD file, 2016-10-11]
10. Frame/10.1 Two Part Frames (for smaller print volumes)/Expansion Frame Two Part A.stl
92.2 x 14.5 x 86.5
