Duds/OI-Piranha/20. Body Lift/Lifting beam.iges

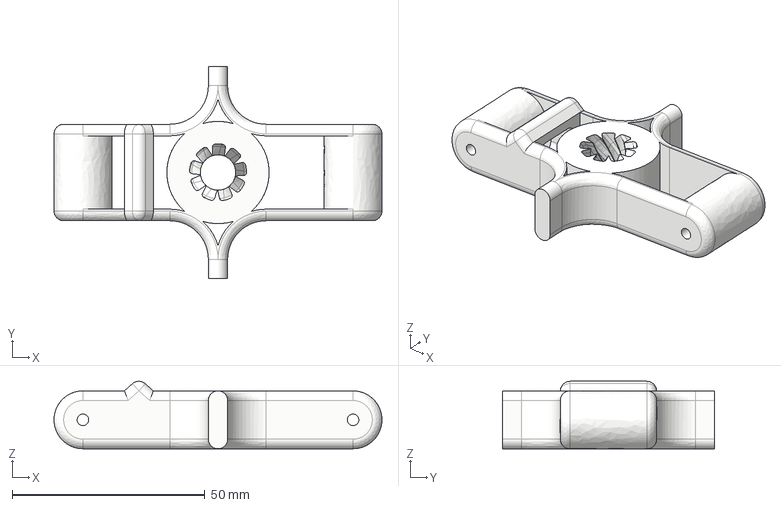
[picture p75: CAD file, 2016-09-26]
20. Body Lift/Lifting beam.iges
85.0 x 55.0 x 17.5 mm
