Duds/OI-Piranha/100. Assembly Analysis/DJI 800 ESC Expansion fitting .png

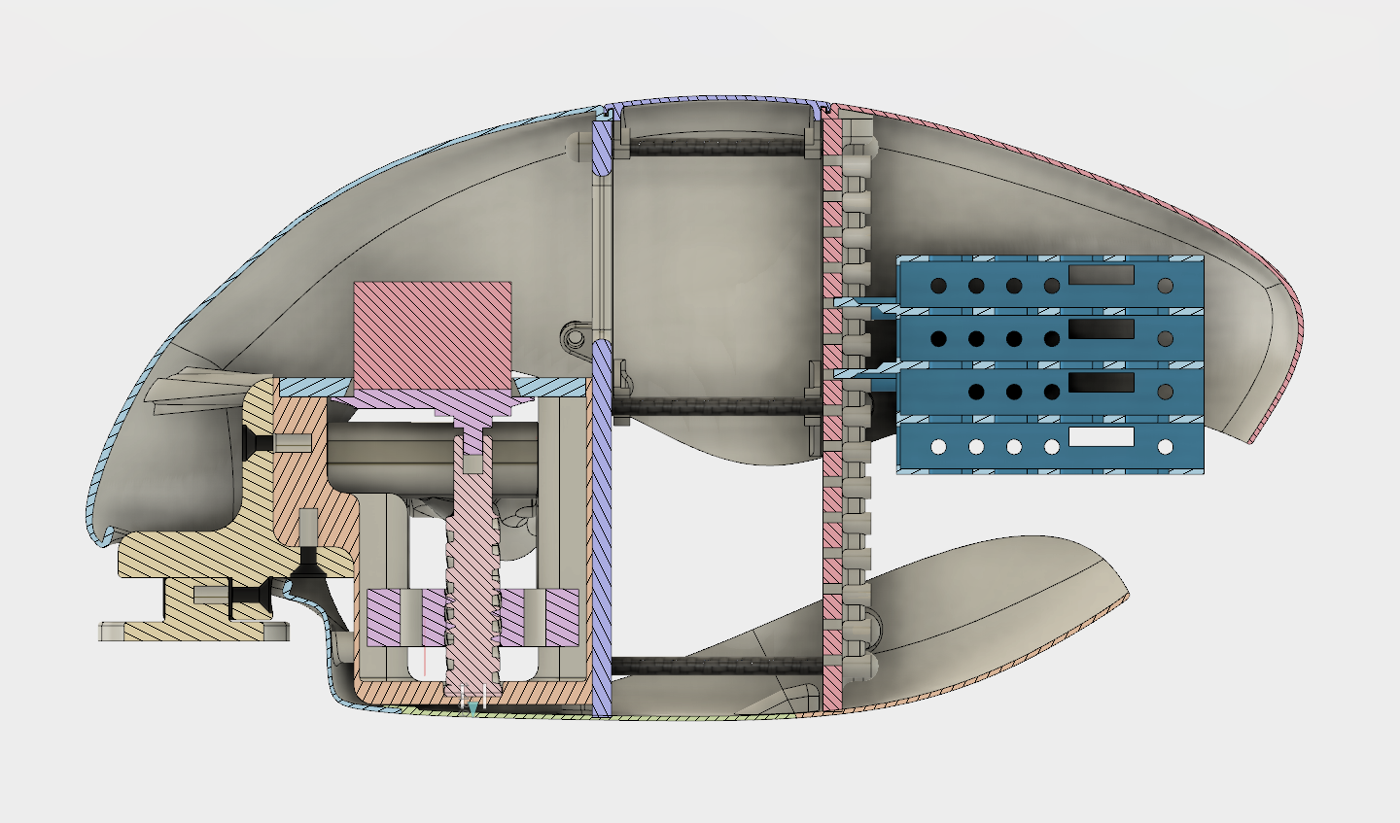
100. Assembly Analysis/DJI 800 ESC Expansion fitting .png
