Duds/OI-Piranha/100. Assembly Analysis/Frame and fairing assembly.png

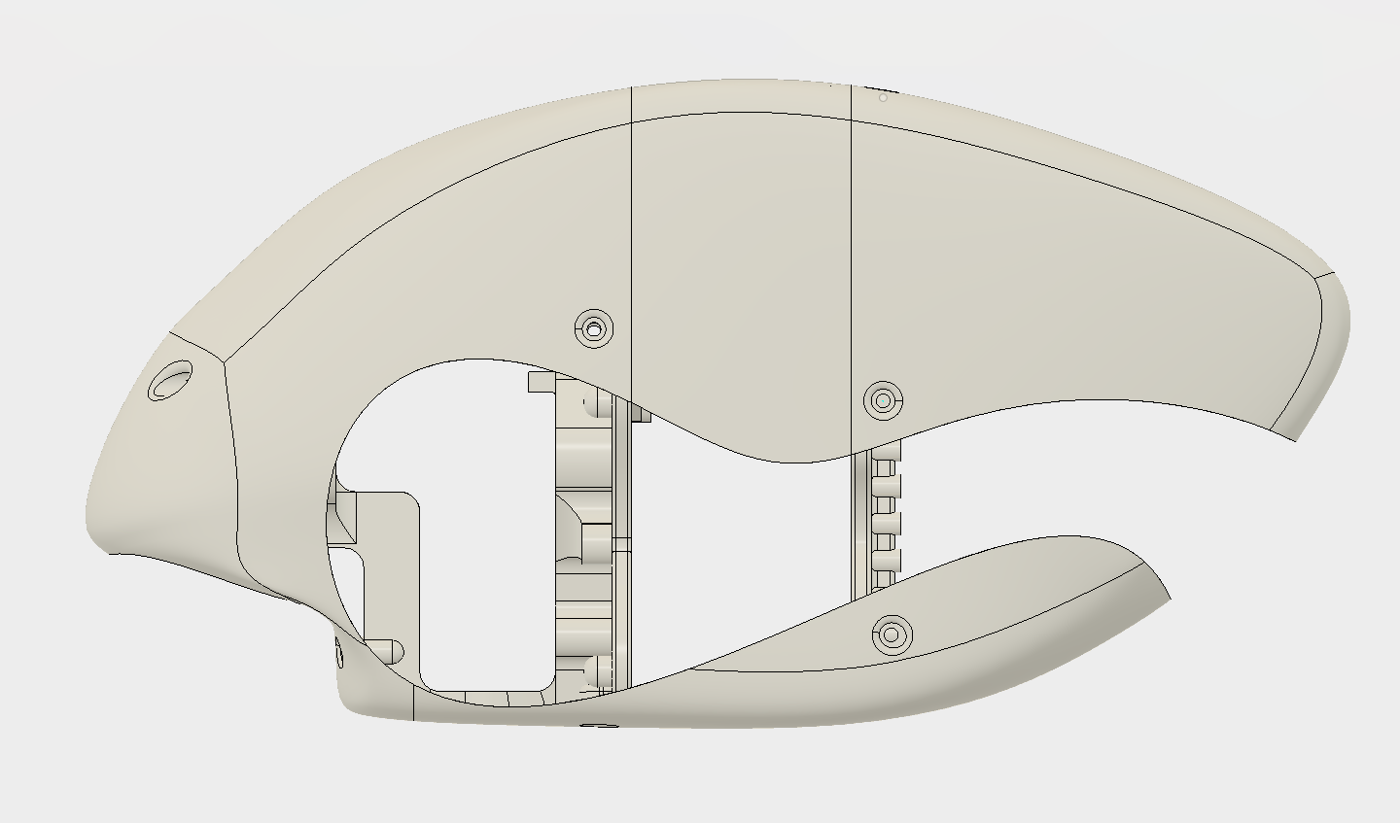
100. Assembly Analysis/Frame and fairing assembly.png
