Duds/OI-Piranha/100. Assembly Analysis/Frame and fairing Section analysis.png

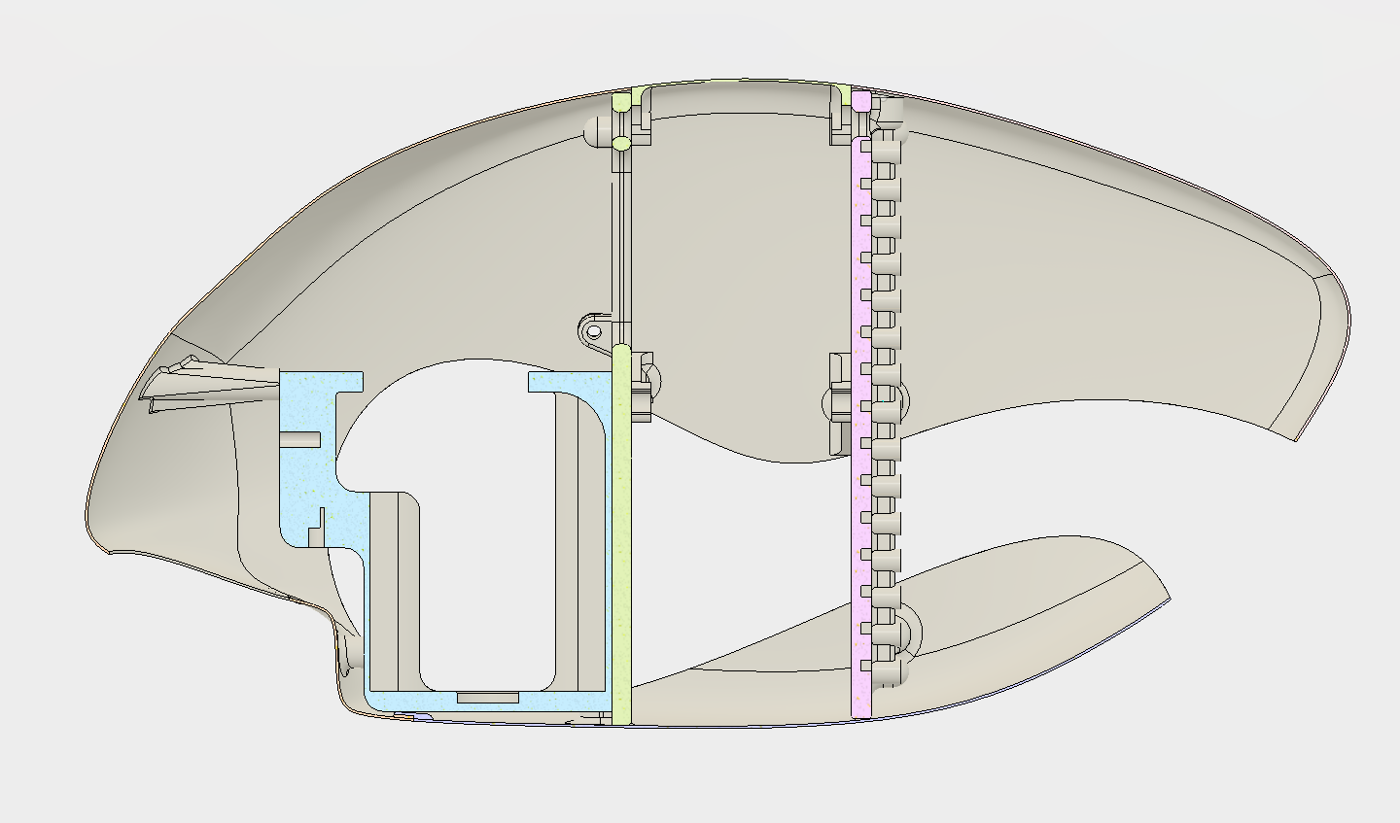
100. Assembly Analysis/Frame and fairing Section analysis.png
