Duds/OI-Piranha/100. Assembly Analysis/Frame, bashplate and expansion fairing assembly.png

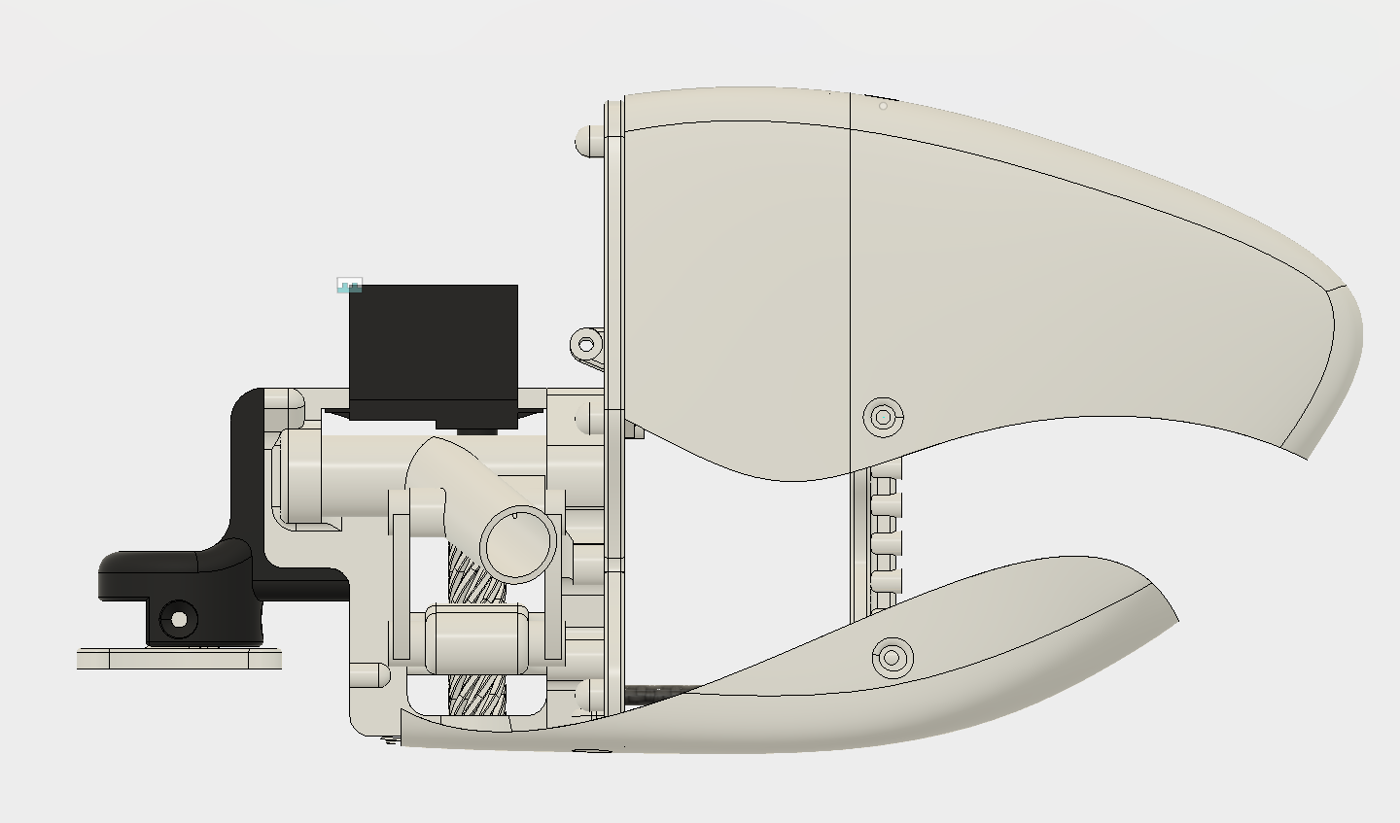
100. Assembly Analysis/Frame, bashplate and expansion fairing assembly.png
