Duds/OI-Piranha/200. Renders/Partial_Assembly_2016-Oct-04_11-30-05PM-000_CustomizedView2153876415.png

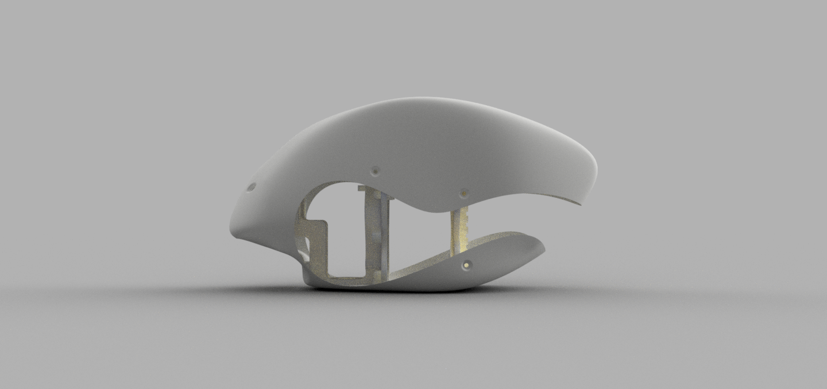
200. Renders/Partial_Assembly_2016-Oct-04_11-30-05PM-000_CustomizedView2153876415.png
