Duds/OI-Piranha/200. Renders/Partial_Assembly_2016-Oct-04_11-30-26PM-000_CustomizedView12868151686.png

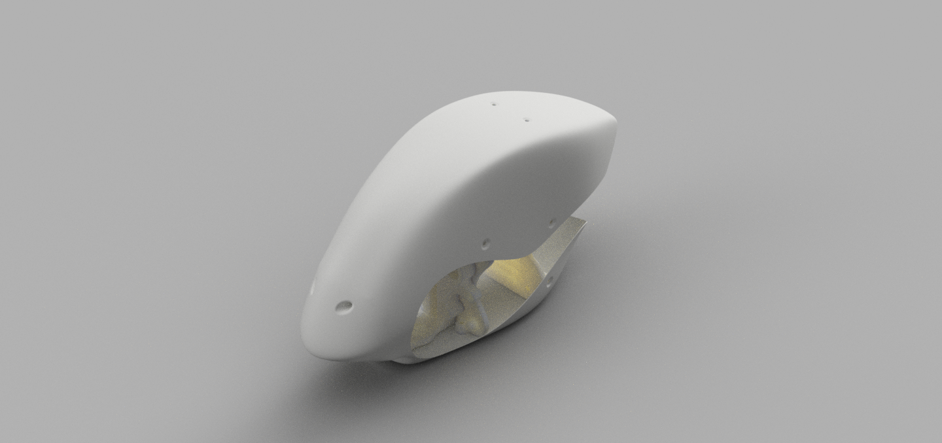
200. Renders/Partial_Assembly_2016-Oct-04_11-30-26PM-000_CustomizedView12868151686.png
