Duds/OI-Piranha/200. Renders/Partial_Assembly_2016-Oct-04_11-31-22PM-000_CustomizedView8560431530.png

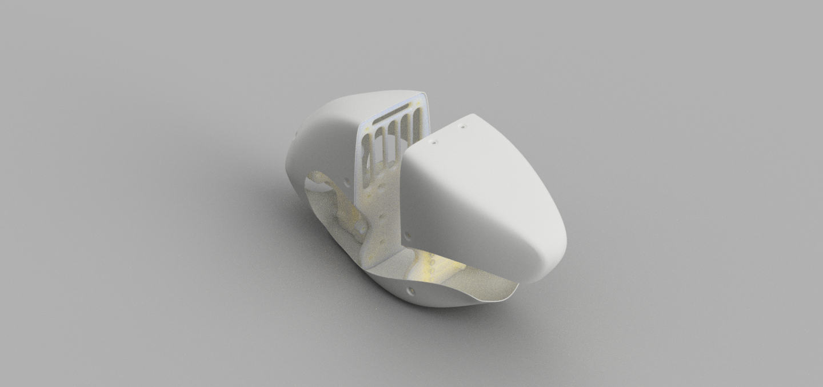
200. Renders/Partial_Assembly_2016-Oct-04_11-31-22PM-000_CustomizedView8560431530.png
