Duds/OI-Piranha/200. Renders/Partial_Assembly_2016-Oct-04_11-34-51PM-000_CustomizedView2961853686.png

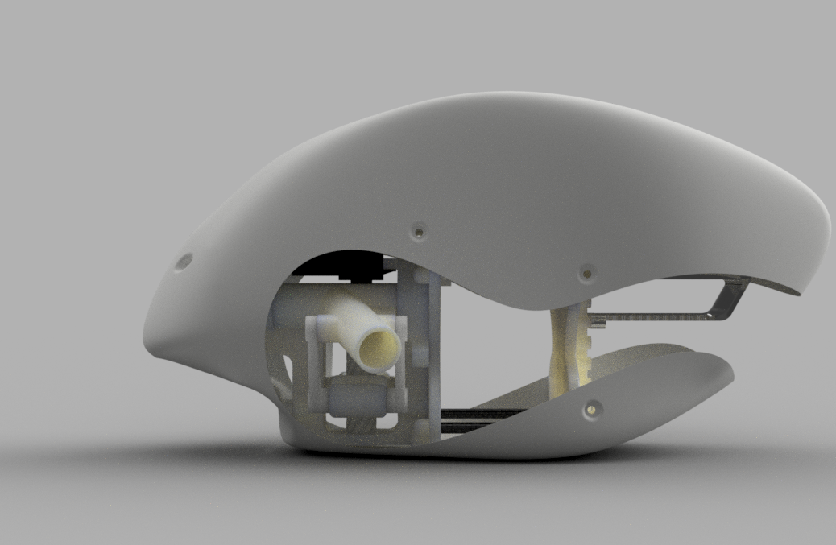
200. Renders/Partial_Assembly_2016-Oct-04_11-34-51PM-000_CustomizedView2961853686.png
