Duds/OI-Piranha/200. Renders/Partial_Assembly_2016-Oct-04_11-35-43PM-000_CustomizedView12097627902.png

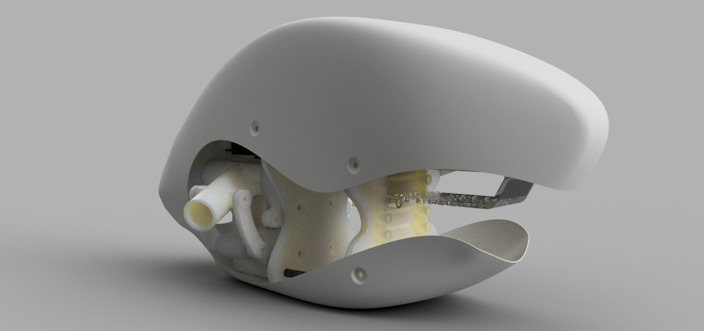
200. Renders/Partial_Assembly_2016-Oct-04_11-35-43PM-000_CustomizedView12097627902.png
